MatanBiton/IOT-Walkie-Talkie/ESP32/wifi_connection.h

#pragma once

namespace WifiConnection {

// Observers are called from the Wi-Fi manager task whenever station
// connectivity returns. Keep callbacks short and non-blocking; they should
// normally wake their owning task or set a reconnect flag.
using ConnectedObserver = void (*)(void* context);

bool begin();
bool ensureConnected();
bool isConnected();

// Enables/disables infrastructure Wi-Fi at runtime. Disabling station
// connectivity stops connection attempts and disconnects from the AP, but the
// WIFI_STA interface remains active so ESP-NOW P2P continues to operate.
bool isEnabled();
void setEnabled(bool enabled);

// Requests a controlled station reconnect from the Wi-Fi manager task. This is
// asynchronous and does not erase credentials.
void requestReconnect(const char* reason);

// Uses a fixed-size observer table and performs no dynamic allocation.
// Registering while already connected schedules one prompt notification.
bool registerConnectedObserver(ConnectedObserver observer, void* context = nullptr);
bool unregisterConnectedObserver(ConnectedObserver observer, void* context = nullptr);

}  // namespace WifiConnection
